limingjie/CH32V003-Soft-Latching-Power-Circuits/schematic/CH32V003_Soft_Latching/CH32V003_Soft_Latching.kicad_sch

## KiCad design schematic/CH32V003_Soft_Latching/CH32V003_Soft_Latching.kicad_sch (2025-04-23)

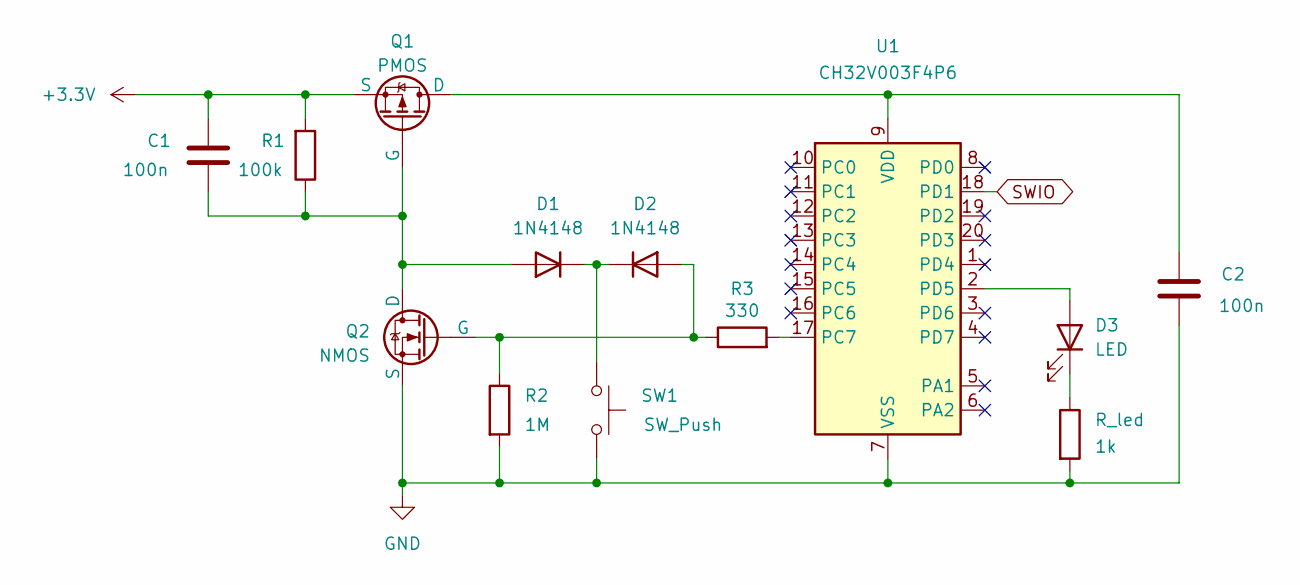
[picture p3: schematic CH32V003_Soft_Latching.kicad_sch]

Parts:
C1, C2: 100n
D1, D2: 1N4148; D_DO-35_SOD27_P7.62mm_Horizontal
D3: LED
Q1: PMOS
Q2: NMOS
R1: 100k
R2: 1M
R3: 330
R_led: 1k
SW1: SW_Push
U1: CH32V003F4P6; TSSOP-20_4.4x6.5mm_P0.65mm

Connections:
+3.3V: C1.1, Q1.3 (S), R1.2
GND: C2.2, Q2.3 (S), R2.2, R_led.2, SW1.1, U1.7 (VSS)
unnamed: C1.2, D1.2 (A), Q1.2 (G), Q2.1 (D), R1.1
unnamed: C2.1, Q1.1 (D), U1.9 (VDD)
unnamed: D1.1 (K), D2.1 (K), SW1.2
unnamed: D2.2 (A), Q2.2 (G), R2.1, R3.1
unnamed: D3.1 (K), R_led.1
unnamed: D3.2 (A), U1.2 (PD5)
unnamed: R3.2, U1.17 (PC7)
SWIO: U1.18 (PD1)
