limingjie/CH32V003-Soft-Latching-Power-Circuits/funconfig.h

#ifndef _FUNCONFIG_H
#define _FUNCONFIG_H

#define CH32V003                  1
#define FUNCONF_SYSTICK_USE_HCLK  1
#define FUNCONF_SYSTEM_CORE_CLOCK 48000000  // Computed Clock in Hz.
#define FUNCONF_USE_DEBUGPRINTF   1

#endif
